Nuto/LoRaTemperatureSensor/src/sensor-v3/bitmaps.h

//Otter
//Prepare Boot Logo 64x56
//https://javl.github.io/image2cpp/
//Background color Transparent
//Horizontal - 1 bit per pixel alpha map
#define BOOT_LOGO_HEIGHT   64
#define BOOT_LOGO_WIDTH    56
const unsigned char bitmap_nager [] PROGMEM = {
  0x00, 0x00, 0x03, 0xff, 0xc0, 0x00, 0x00, 0x03, 0xf8, 0x3f, 0xff, 0xfc, 0x1f, 0xc0, 0x07, 0xfe,
  0xff, 0xff, 0xff, 0x7f, 0xe0, 0x0f, 0xff, 0xf8, 0x00, 0x1f, 0xff, 0xf0, 0x1f, 0x9f, 0xc0, 0x00,
  0x03, 0xf9, 0xf8, 0x1e, 0x1f, 0x00, 0x00, 0x00, 0xf8, 0x78, 0x1e, 0x3c, 0x00, 0x00, 0x00, 0x3c,
  0x78, 0x3c, 0x78, 0x00, 0x00, 0x00, 0x1e, 0x3c, 0x3c, 0xf0, 0x00, 0x00, 0x00, 0x0f, 0x3c, 0x3d,
  0xe0, 0x00, 0x00, 0x00, 0x07, 0xbc, 0x3f, 0xc0, 0x00, 0x00, 0x00, 0x03, 0xfc, 0x1f, 0x80, 0x00,
  0x00, 0x00, 0x01, 0xf8, 0x1f, 0x00, 0x00, 0x00, 0x00, 0x00, 0xf8, 0x1e, 0x00, 0x00, 0x00, 0x00,
  0x00, 0x78, 0x1e, 0x00, 0x00, 0x00, 0x00, 0x00, 0x78, 0x1c, 0x00, 0x00, 0x00, 0x00, 0x00, 0x38,
  0x38, 0x00, 0x00, 0x00, 0x00, 0x00, 0x1c, 0x38, 0x00, 0x00, 0x00, 0x00, 0x00, 0x1c, 0x70, 0x01,
  0xc0, 0x00, 0x01, 0x00, 0x0e, 0x70, 0x03, 0xe0, 0x00, 0x07, 0xc0, 0x0e, 0x70, 0x03, 0xe0, 0x00,
  0x07, 0xc0, 0x0e, 0xe0, 0x03, 0xe0, 0x00, 0x07, 0xc0, 0x07, 0xe0, 0x03, 0xe0, 0x00, 0x07, 0xc0,
  0x07, 0xe0, 0x03, 0xe0, 0x00, 0x07, 0xc0, 0x07, 0xe0, 0x03, 0xe0, 0x00, 0x07, 0xc0, 0x07, 0xe0,
  0x03, 0xe0, 0x00, 0x07, 0xc0, 0x07, 0xe0, 0x03, 0xe0, 0x00, 0x07, 0xc0, 0x07, 0xe0, 0x03, 0xe0,
  0x00, 0x07, 0xc0, 0x07, 0xe0, 0x01, 0xc0, 0x00, 0x03, 0xc0, 0x07, 0xe0, 0x00, 0x00, 0x00, 0x00,
  0x00, 0x07, 0xe0, 0x00, 0x01, 0xff, 0x80, 0x00, 0x07, 0xe0, 0x00, 0x03, 0xff, 0xc0, 0x00, 0x07,
  0xe0, 0x00, 0x07, 0xff, 0xf0, 0x00, 0x07, 0xe0, 0x07, 0xff, 0xff, 0xff, 0xe0, 0x07, 0xe0, 0x1c,
  0x0f, 0xff, 0xf8, 0x18, 0x07, 0xe0, 0x60, 0x0f, 0xff, 0xf0, 0x06, 0x07, 0xe0, 0xc0, 0x0f, 0xff,
  0xf0, 0x03, 0x07, 0xe0, 0x80, 0x07, 0xff, 0xe0, 0x01, 0x07, 0xe1, 0x80, 0x03, 0xff, 0xc0, 0x00,
  0x87, 0xe1, 0x00, 0x00, 0xff, 0x00, 0x00, 0x87, 0xe1, 0x00, 0x00, 0x18, 0x00, 0x00, 0xc7, 0xe3,
  0x00, 0x00, 0x18, 0x00, 0x00, 0x47, 0xe3, 0x00, 0x00, 0x18, 0x00, 0x00, 0x47, 0xe3, 0x01, 0x00,
  0x18, 0x00, 0xc0, 0x47, 0xe3, 0x00, 0xc0, 0x3c, 0x01, 0x80, 0x47, 0xe3, 0x00, 0x60, 0x66, 0x07,
  0x00, 0x47, 0xe3, 0x00, 0x39, 0xc1, 0x8c, 0x00, 0x47, 0xe3, 0x00, 0x0f, 0x00, 0xf0, 0x00, 0x47,
  0xe3, 0x00, 0x00, 0x00, 0x00, 0x00, 0x47, 0xe3, 0x00, 0x00, 0x00, 0x00, 0x00, 0x47, 0xe3, 0x00,
  0x00, 0x00, 0x00, 0x00, 0x47, 0xe3, 0x00, 0x00, 0x00, 0x00, 0x00, 0x47, 0xe3, 0x00, 0x00, 0x00,
  0x00, 0x00, 0x47, 0xe3, 0x00, 0x00, 0x00, 0x00, 0x00, 0x47, 0xe3, 0x00, 0x00, 0x00, 0x00, 0x00,
  0x47, 0xe3, 0x00, 0x00, 0x00, 0x00, 0x00, 0x47, 0xe3, 0x00, 0x00, 0x00, 0x00, 0x00, 0x47, 0xe3,
  0x00, 0x00, 0x00, 0x00, 0x00, 0x47, 0xe3, 0x00, 0x00, 0x00, 0x00, 0x00, 0x47, 0xe3, 0x00, 0x00,
  0x00, 0x00, 0x00, 0x47, 0xe3, 0x00, 0x00, 0x00, 0x00, 0x00, 0x47, 0xe3, 0x00, 0x00, 0x00, 0x00,
  0x00, 0x47, 0xe2, 0x00, 0x00, 0x00, 0x00, 0x00, 0x47, 0xc0, 0x00, 0x00, 0x00, 0x00, 0x00, 0x03
};
